fhnw-sgi-ip12-23vt/Ip12-23vt_powerhouse/docu/software(sad)/images/Ebene1.drawio.png

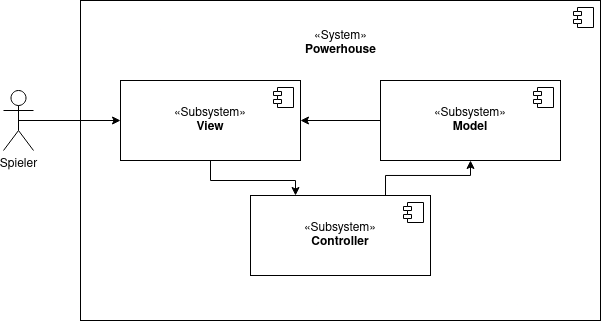
docu/software(sad)/images/Ebene1.drawio.png
