fhnw-sgi-ip12-23vt/Ip12-23vt_powerhouse/energieeffizienz-sourcecode/src/main/resources/img/Elektronix/Titelbild.png

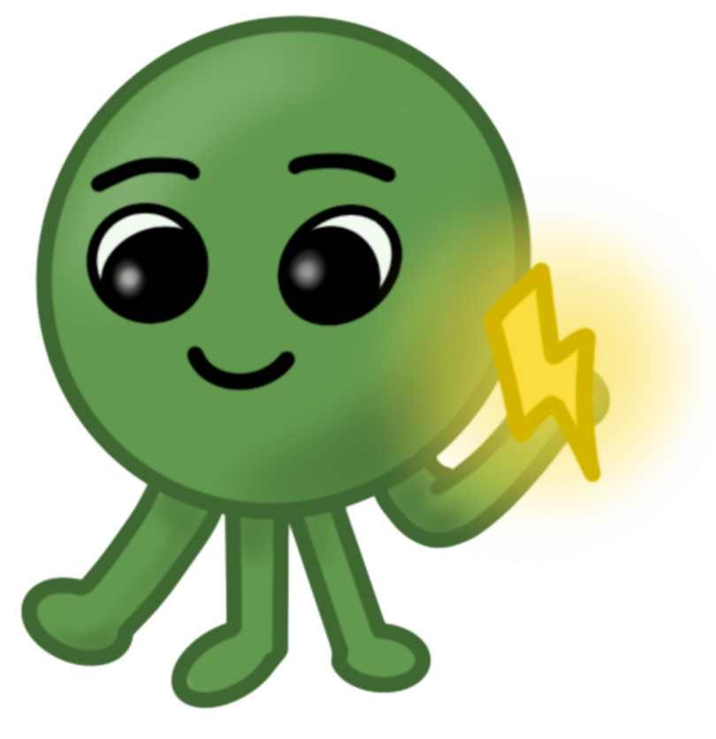
energieeffizienz-sourcecode/src/main/resources/img/Elektronix/Titelbild.png
