fhnw-sgi-ip12-23vt/Ip12-23vt_powerhouse/docu/hardware/3D-Objekte Dateien/Transparente Objekte/Lampe.stl

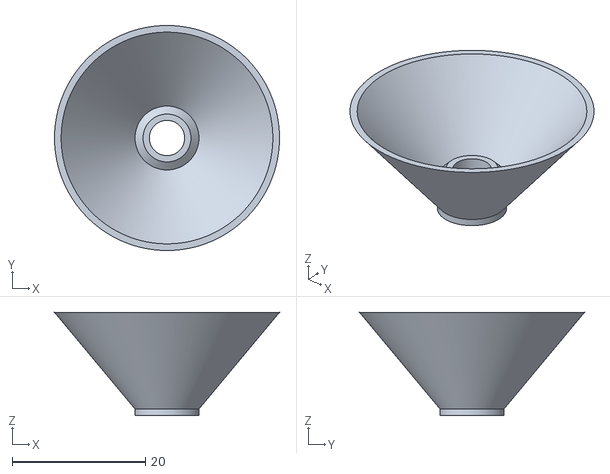
[picture p51: CAD file, 2024-06-05]
docu/hardware/3D-Objekte Dateien/Transparente Objekte/Lampe.stl
33.8 x 33.8 x 15.5
