fhnw-sgi-ip12-23vt/Ip12-23vt_powerhouse/docu/hardware/3D-Objekte Dateien/Weitere Objekte/Küche/Küchenschranktüre.stl

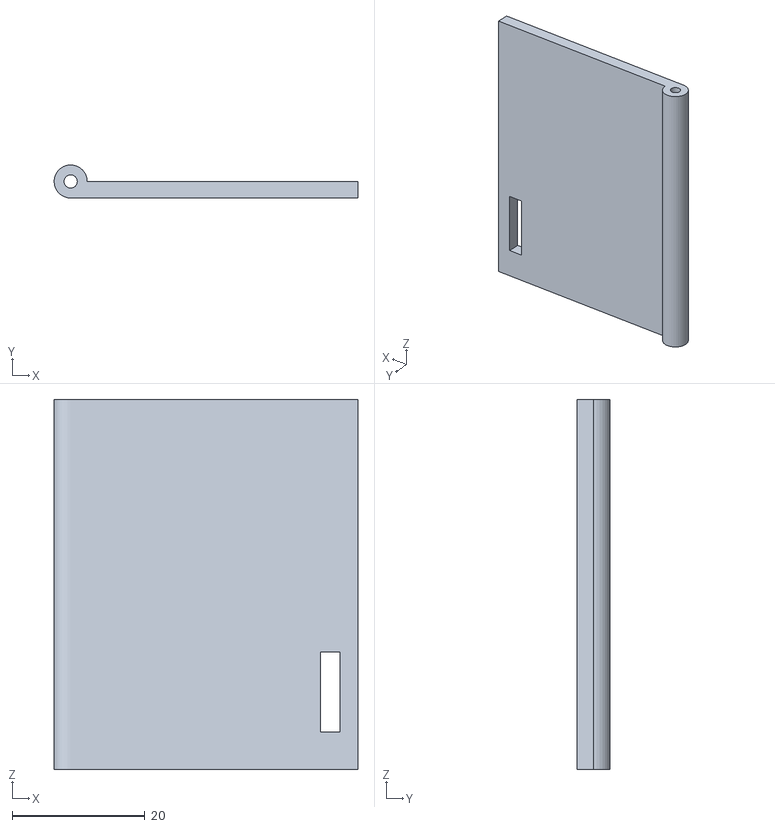
[picture p52: CAD file, 2024-06-05]
docu/hardware/3D-Objekte Dateien/Weitere Objekte/Küche/Küchenschranktüre.stl
45.8 x 5.00 x 55.8
