fhnw-sgi-ip12-23vt/Ip12-23vt_powerhouse/docu/hardware/3D-Objekte Dateien/Weitere Objekte/Schlafzimmer/Nachttisch.stl

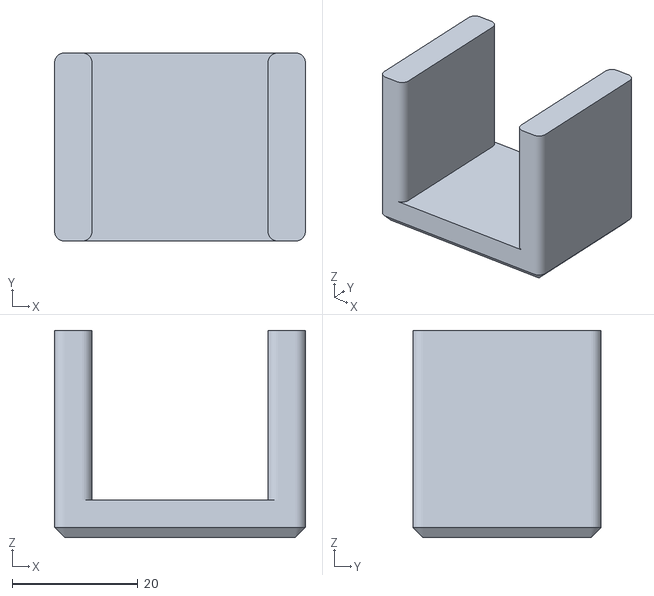
[picture p53: CAD file, 2024-06-05]
docu/hardware/3D-Objekte Dateien/Weitere Objekte/Schlafzimmer/Nachttisch.stl
40.0 x 30.0 x 33.0
