fhnw-sgi-ip12-23vt/Ip12-23vt_powerhouse/docu/hardware/3D-Objekte Dateien/Weitere Objekte/Wohnzimmer/Fernsehtisch.stl

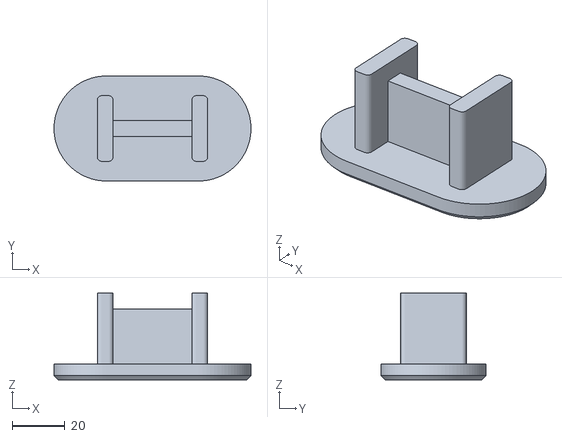
[picture p54: CAD file, 2024-06-05]
docu/hardware/3D-Objekte Dateien/Weitere Objekte/Wohnzimmer/Fernsehtisch.stl
75.0 x 40.0 x 33.0
