fhnw-sgi-ip12-23vt/Ip12-23vt_powerhouse/docu/hardware/3D-Objekte Dateien/Weitere Objekte/Küche/Küchenschrank.stl

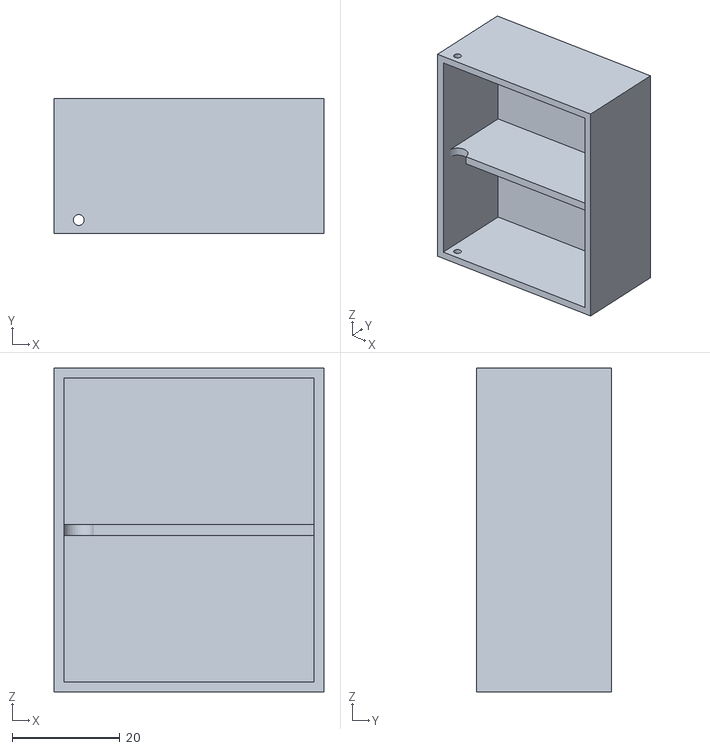
[picture p55: CAD file, 2024-06-05]
docu/hardware/3D-Objekte Dateien/Weitere Objekte/Küche/Küchenschrank.stl
50.0 x 25.0 x 60.0
