fhnw-sgi-ip12-23vt/Ip12-23vt_powerhouse/docu/hardware/3D-Objekte Dateien/Weitere Objekte/Schlafzimmer/Bürotisch.stl

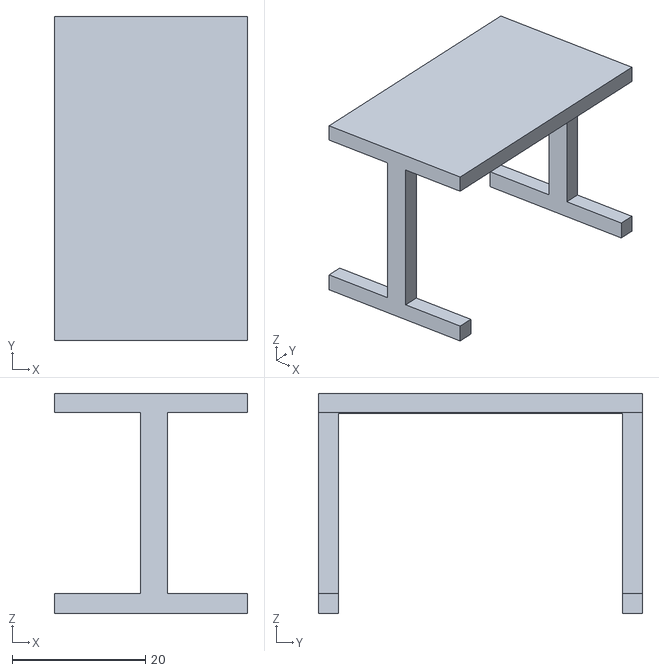
[picture p56: CAD file, 2024-06-05]
docu/hardware/3D-Objekte Dateien/Weitere Objekte/Schlafzimmer/Bürotisch.stl
29.0 x 48.6 x 33.0
