fhnw-sgi-ip12-23vt/Ip12-23vt_powerhouse/docu/hardware/3D-Objekte Dateien/Weitere Objekte/Wohnzimmer/Aquarium_Deckel.stl

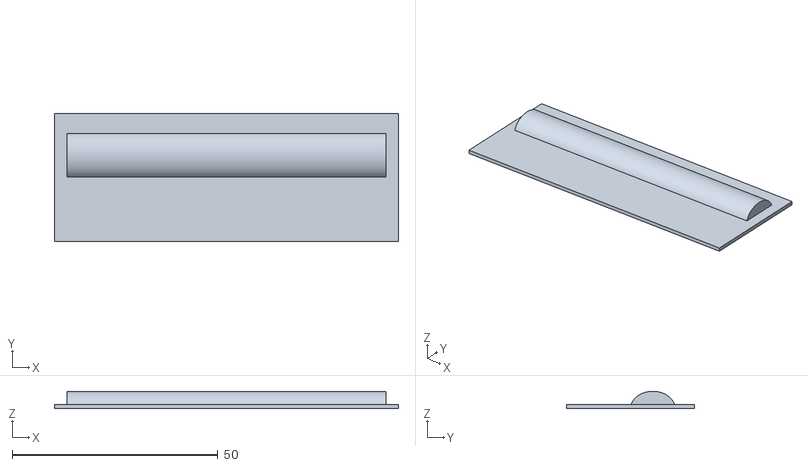
[picture p57: CAD file, 2024-06-05]
docu/hardware/3D-Objekte Dateien/Weitere Objekte/Wohnzimmer/Aquarium_Deckel.stl
83.5 x 31.0 x 4.23
