fhnw-sgi-ip12-23vt/Ip12-23vt_powerhouse/docu/hardware/3D-Objekte Dateien/Weitere Objekte/Küche/Küche_Waschbecken.stl

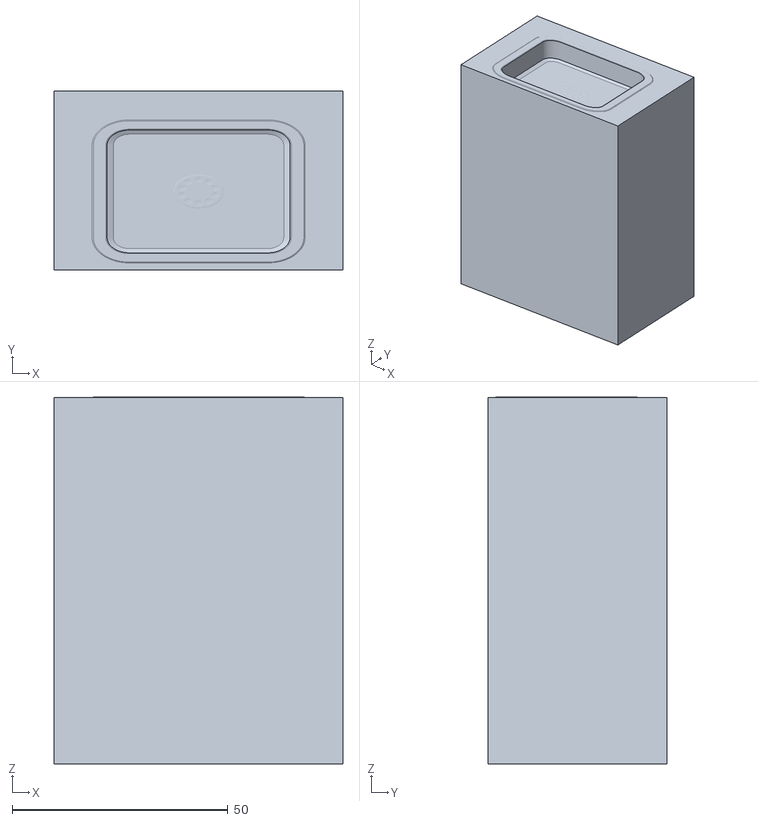
[picture p58: CAD file, 2024-06-05]
docu/hardware/3D-Objekte Dateien/Weitere Objekte/Küche/Küche_Waschbecken.stl
66.8 x 41.5 x 85.0
