fhnw-sgi-ip12-23vt/Ip12-23vt_powerhouse/docu/hardware/3D-Objekte Dateien/Weitere Objekte/Wohnzimmer/Sofa.stl

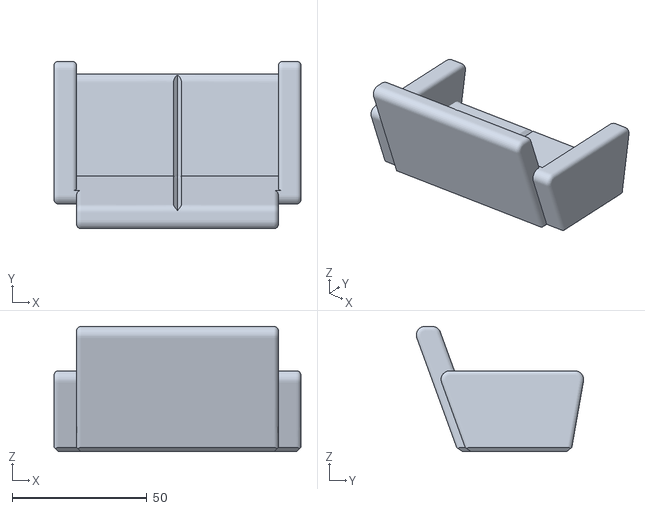
[picture p59: CAD file, 2024-06-05]
docu/hardware/3D-Objekte Dateien/Weitere Objekte/Wohnzimmer/Sofa.stl
91.8 x 62.2 x 46.5
