fhnw-sgi-ip12-23vt/Ip12-23vt_powerhouse/docu/hardware/3D-Objekte Dateien/Weitere Objekte/Wohnzimmer/Bücherregal.stl

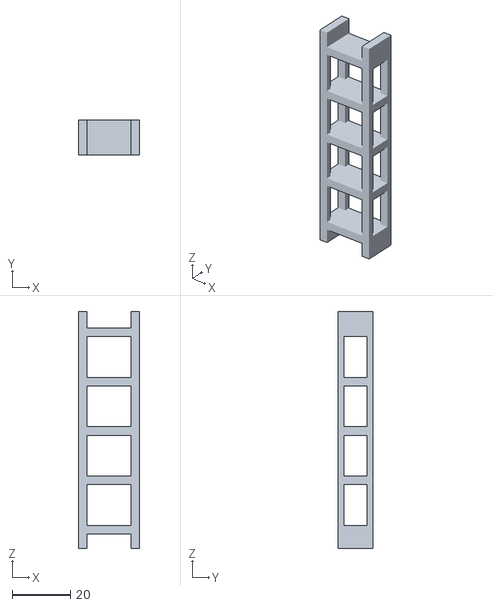
[picture p60: CAD file, 2024-06-05]
docu/hardware/3D-Objekte Dateien/Weitere Objekte/Wohnzimmer/Bücherregal.stl
21.0 x 11.9 x 81.7
