fhnw-sgi-ip12-23vt/Ip12-23vt_powerhouse/docu/hardware/3D-Objekte Dateien/Weitere Objekte/Wohnzimmer/Aquarium_Rahmen.stl

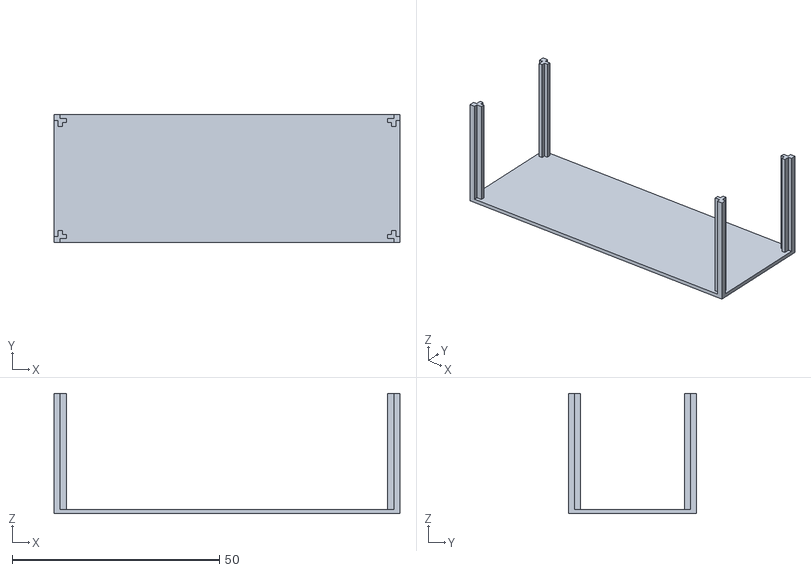
[picture p61: CAD file, 2024-06-05]
docu/hardware/3D-Objekte Dateien/Weitere Objekte/Wohnzimmer/Aquarium_Rahmen.stl
83.5 x 31.0 x 29.0
